furyou81/crypto_transfer/PIC32CRYPTO/types.h

/*
 * File:   types.h
 * Author: bocal
 *
 * Created on March 22, 2018, 11:06 AM
 */

#ifndef TYPES_H
#define	TYPES_H

typedef unsigned char u8;
typedef unsigned short u16;
typedef unsigned long u32;
typedef signed char s8;
typedef signed short s16;
typedef signed long s32;

#ifdef	__cplusplus
extern "C" {
#endif




#ifdef	__cplusplus
}
#endif

#endif	/* TYPES_H */
